trdenton/humsensor/hum_sw/humtx/mirf.c

/*
    Copyright (c) 2007 Stefan Engelke <mbox@stefanengelke.de>

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
    $Id$
*/

#include "mirf.h"
#include "nRF24L01.h"
#include "spi.h"
#include <avr/io.h>
#include <avr/interrupt.h>

// Defines for setting the MiRF registers for transmitting or receiving mode
#define TX_POWERUP mirf_config_register(CONFIG, mirf_CONFIG | ( (1<<PWR_UP) | (0<<PRIM_RX) ) )
#define RX_POWERUP mirf_config_register(CONFIG, mirf_CONFIG | ( (1<<PWR_UP) | (1<<PRIM_RX) ) )


// Flag which denotes transmitting mode
volatile uint8_t PTX;

void mirf_init() 
// Initializes pins ans interrupt to communicate with the MiRF module
// Should be called in the early initializing phase at startup.
{
    // Define CSN and CE as Output and set them to default
    DDRA |= ((1<<CSN)|(1<<CE));
    mirf_CE_lo;
    mirf_CSN_hi;

    // Initialize external interrupt on port PB5 (PCINT13)
    DDRB &= ~(1<<PB6);
    PCMSK1 = (1<<PCINT13);
    PCICR  = (1<<PCIE1);

    // Initialize spi module
    spi_init();
}


void mirf_config() 
// Sets the important registers in the MiRF module and powers the module
// in receiving mode
{
    // Set RF channel
    mirf_config_register(RF_CH,mirf_CH);

    // Set length of incoming payload 
    mirf_config_register(RX_PW_P0, mirf_PAYLOAD);

    mirf_config_register(FEATURE,(1<<EN_DYN_ACK));
    //disable Auto retransmit, auto ack
    mirf_config_register(EN_AA,0x00);	
    mirf_config_register(SETUP_RETR,0x00);    
    //mirf_config_register(DYNPD,0x00);    

    //set transmit address
    uint8_t addr[] = {'a','b','c','d','e'};
    mirf_set_TADDR(addr);

    //set data rate to lowest

    mirf_config_register(RF_SETUP,(1<<RF_DR_LOW) | (2<<RF_PWR));

    // Start receiver 
    PTX = 0;        // Start in receiving mode
    RX_POWERUP;     // Power up in receiving mode
    mirf_CE_hi;     // Listening for pakets
}

void mirf_set_RADDR(uint8_t * adr) 
// Sets the receiving address
{
    mirf_CE_lo;
    mirf_write_register(RX_ADDR_P0,adr,5);
    mirf_CE_hi;
}

void mirf_set_TADDR(uint8_t * adr)
// Sets the transmitting address
{
    mirf_write_register(TX_ADDR, adr,5);
}


ISR(PCINT1_vect)
// Interrupt handler 
{
	uint8_t status;   
	// If still in transmitting mode then finish transmission
	if (PTX) {

		// Read MiRF status 
		mirf_CSN_lo;                                // Pull down chip select
		status = spi_fast_shift(NOP);               // Read status register
		mirf_CSN_hi;                                // Pull up chip select

		mirf_CE_lo;                             // Deactivate transreceiver
		RX_POWERUP;                             // Power up in receiving mode
		mirf_CE_hi;                             // Listening for pakets
		PTX = 0;                                // Set to receiving mode

		// Reset status register for further interaction
		mirf_config_register(STATUS,(1<<TX_DS)|(1<<MAX_RT)); // Reset status register
	}
}

extern uint8_t mirf_data_ready() 
// Checks if data is available for reading
{
    if (PTX) return 0;
    uint8_t status;
    // Read MiRF status 
    mirf_CSN_lo;                                // Pull down chip select
    status = spi_fast_shift(NOP);               // Read status register
    mirf_CSN_hi;                                // Pull up chip select
    return status & (1<<RX_DR);
}

extern void mirf_get_data(uint8_t * data) 
// Reads mirf_PAYLOAD bytes into data array
{
    mirf_CSN_lo;                               // Pull down chip select
    spi_fast_shift( R_RX_PAYLOAD );            // Send cmd to read rx payload
    spi_transfer_sync(data,data,mirf_PAYLOAD); // Read payload
    mirf_CSN_hi;                               // Pull up chip select
    mirf_config_register(STATUS,(1<<RX_DR));   // Reset status register
}

void mirf_config_register(uint8_t reg, uint8_t value)
// Clocks only one byte into the given MiRF register
{
    mirf_CSN_lo;
    spi_fast_shift(W_REGISTER | (REGISTER_MASK & reg));
    spi_fast_shift(value);
    mirf_CSN_hi;
}

void mirf_read_register(uint8_t reg, uint8_t * value, uint8_t len)
// Reads an array of bytes from the given start position in the MiRF registers.
{
    mirf_CSN_lo;
    spi_fast_shift(R_REGISTER | (REGISTER_MASK & reg));
    spi_transfer_sync(value,value,len);
    mirf_CSN_hi;
}

void mirf_write_register(uint8_t reg, uint8_t * value, uint8_t len) 
// Writes an array of bytes into inte the MiRF registers.
{
    mirf_CSN_lo;
    spi_fast_shift(W_REGISTER | (REGISTER_MASK & reg));
    spi_transmit_sync(value,len);
    mirf_CSN_hi;
}


void mirf_send(uint8_t * value, uint8_t len) 
// Sends a data package to the default address. Be sure to send the correct
// amount of bytes as configured as payload on the receiver.
{
    while (PTX) {}                  // Wait until last paket is send

    mirf_CE_lo;

    PTX = 1;                        // Set to transmitter mode
    TX_POWERUP;                     // Power up
    
    mirf_CSN_lo;                    // Pull down chip select
    spi_fast_shift( FLUSH_TX );     // Write cmd to flush tx fifo
    mirf_CSN_hi;                    // Pull up chip select
    
    mirf_CSN_lo;                    // Pull down chip select
    spi_fast_shift( W_TX_PAYLOAD_NO_ACK ); // Write cmd to write payload
    spi_transmit_sync(value,len);   // Write payload
    mirf_CSN_hi;                    // Pull up chip select
    
    mirf_CE_hi;                     // Start transmission
}
